SolderedElectronics/Air-quality-sensor-CCS811-breakout-hardware-design/OUTPUTS/V1.1.1/Air quality sensor CCS811 breakout Pinout.jpg

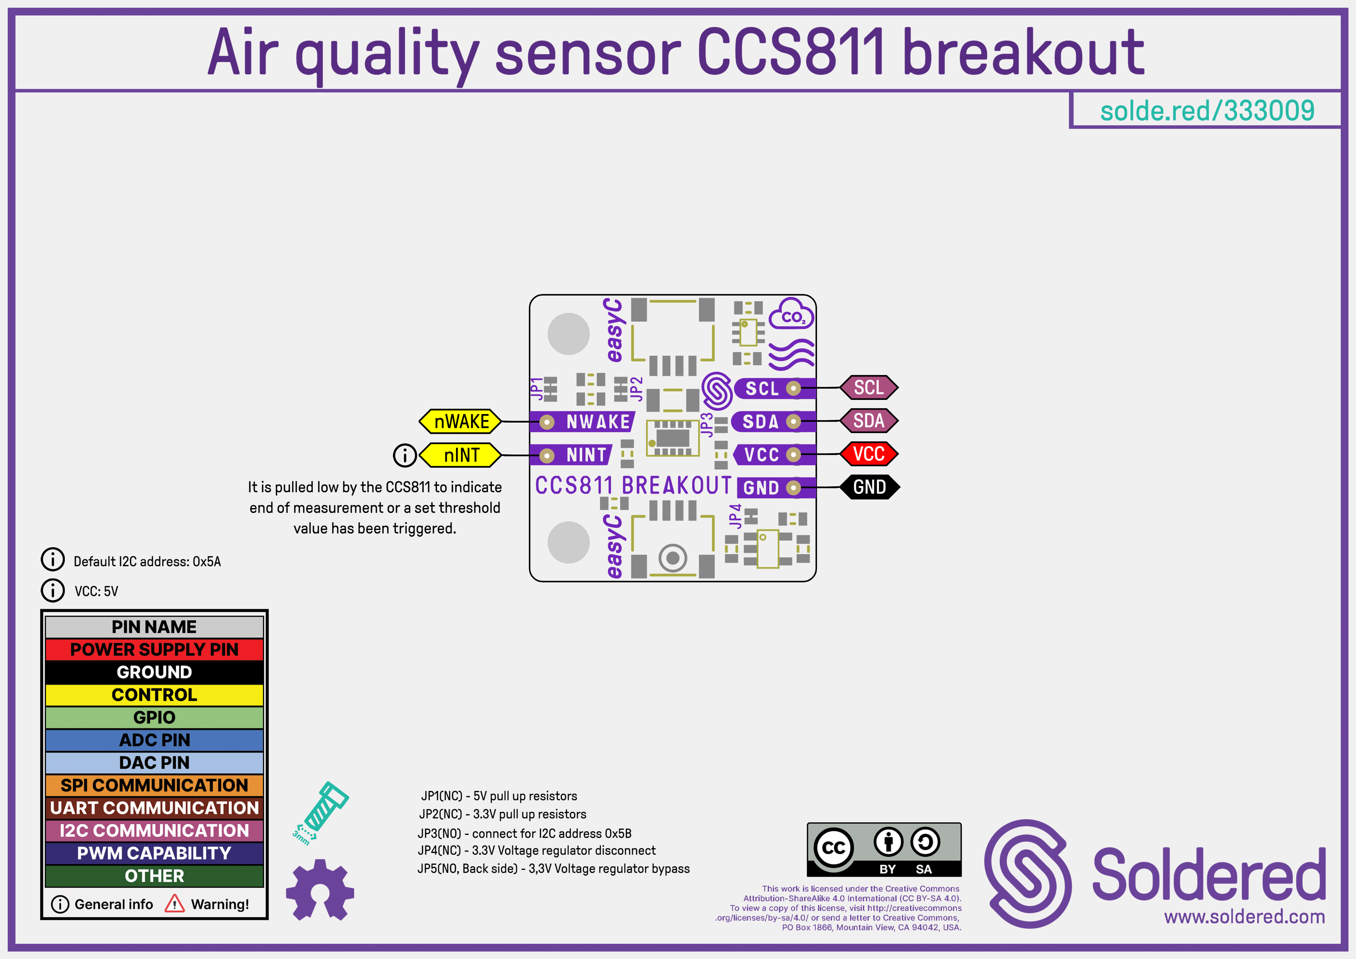
OUTPUTS/V1.1.1/Air quality sensor CCS811 breakout Pinout.jpg
